CTXz/Not-so-Tiny-Dimmer/src/strip.h

          /*
   * Copyright (C) 2020  Patrick Pedersen

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
   * Author: Patrick Pedersen <ctx.xda@gmail.com>
   * Description: Exposes hardware abstraction routines for the LED strip.
   * 
   */

#pragma once

#include <stdbool.h>
#include <stdint.h>

#include <avr/eeprom.h>

#include "config.h"

#define R 0
#define G 1
#define B 2

#define RGB 0
#define GRB 1
#define BRG 2
#define BGR 3

#if STRIP_TYPE == WS2812

        extern uint16_t eeprom_strip_size EEMEM;
        extern uint16_t strip_size;

        #define SET_STRIP_SIZE(size) eeprom_update_word(&eeprom_strip_size, size)
        
        #ifdef STRIP_SIZE
                #define GET_STRIP_SIZE STRIP_SIZE
        #else
                #define GET_STRIP_SIZE (eeprom_read_word(&eeprom_strip_size))
        #endif
        
        #if WS2812_COLOR_ORDER == RGB
                #define WS2812_WIRING_RGB_0 0
                #define WS2812_WIRING_RGB_1 1
                #define WS2812_WIRING_RGB_2 2
        #elif WS2812_COLOR_ORDER == GRB
                #define WS2812_WIRING_RGB_0 1
                #define WS2812_WIRING_RGB_1 0
                #define WS2812_WIRING_RGB_2 2
        #elif WS2812_COLOR_ORDER == BRG
                #define WS2812_WIRING_RGB_0 2
                #define WS2812_WIRING_RGB_1 0
                #define WS2812_WIRING_RGB_2 1
        #elif WS2812_COLOR_ORDER == BGR
                #define WS2812_WIRING_RGB_0 2
                #define WS2812_WIRING_RGB_1 1
                #define WS2812_WIRING_RGB_2 0
        #else
                #error "No color order specified! Please set the WS2812_COLOR_ORDER directive in the config file!"
        #endif

#else

        #if NON_ADDR_STRIP_R == PB0
                #define NON_ADDR_STRIP_R_OCR OCR0A
        #elif NON_ADDR_STRIP_R == PB1
                #define NON_ADDR_STRIP_R_OCR OCR0B
        #elif NON_ADDR_STRIP_R == PB4
                #define NON_ADDR_STRIP_R_OCR OCR1B
        #else
                #error "Red LED pin does not support PWM! Please use PB0, PB1 or PB4!"
        #endif

        #if NON_ADDR_STRIP_G == PB0
                #define NON_ADDR_STRIP_G_OCR OCR0A
        #elif NON_ADDR_STRIP_G == PB1
                #define NON_ADDR_STRIP_G_OCR OCR0B
        #elif NON_ADDR_STRIP_G == PB4
                #define NON_ADDR_STRIP_G_OCR OCR1B
        #else
                #error "Green LED pin does not support PWM! Please use PB0, PB1 or PB4!"
        #endif

        #if NON_ADDR_STRIP_B == PB0
                #define NON_ADDR_STRIP_B_OCR OCR0A
        #elif NON_ADDR_STRIP_B == PB1
                #define NON_ADDR_STRIP_B_OCR OCR0B
        #elif NON_ADDR_STRIP_B == PB4
                #define NON_ADDR_STRIP_B_OCR OCR1B
        #else
                #error "Blue LED pin does not support PWM! Please use PB0, PB1 or PB4!"
        #endif

#endif

////////////////////////
// Data Structures
////////////////////////

/* RGB_t
 * ----------
 * Description:
 *      A simple three byte long array that
 *      stores RGB color values.
 */
typedef uint8_t RGB_t[3];
typedef uint8_t* RGB_ptr_t;

/* RGBbuf
 * ----------
 * Description:
 *      A primitve array of RGB_t objects.
 *      Must be allocated first! To project
 *      RGB buffers onto the stirp, use
 *      strip_apply_RGBbuf.
 * 
 *      WARNING: RGB buffers are very memory intensive,
 *      especially on bigger strips. Please consider using 
 *      other data structures if possible! If access of single
 *      pixels is required, please consider using the pxlbuf data
 *      structure!
 *      
 *      The required memory for a RGB buffer is given by:
 * 
 *              mem = RGB buffer size * sizeof(RGB_t) = RGB buffer size * 3
 * 
 *      Meaning if one were to fill a strip of 100 pixels with a RGB buffer, a
 *      total of 300 Bytes of memory would be necessary. This, toghether with
 *      the required memory for the firmware would exceed an ATtiny's memory
 *      size.  
 *            
 */
typedef RGB_t* RGBbuf;

/* substrp
 * ----------
 * Description:
 *      Reverses a given amount of pixels (length) and sets them
 *      to a specific color (rgb).
 *            
 */
typedef struct substrp {
        uint16_t length;
        RGB_t rgb;
} substrp;

/* substrpbuf
 * ----------
 * Description:
 *      Buffer of substrips. Substrips are projected
 *      in their indexed order. If the substrips do
 *      not cover the entire strip, the remaining
 *      pixels are set to off.
 *      Must be allocated first!
 * 
 *      Also see:
 *              substrpbuf_cpy
 *              substrpbuf_free
 *            
 */
typedef struct substrpbuf {
        uint16_t n_substrps;
        substrp *substrps;
} substrpbuf;

/* pxl
 * ----------
 * Description:
 *      Addresses a pixel at any given position (pos)
 *      and sets its color to the provided RGB value (rgb).
 *            
 */
typedef struct pxl {
        uint16_t pos;
        RGB_t rgb;
} pxl;

/* pxlbuf
 * ----------
 * Description:
 *      Buffer of pxl objects. Allows one to address
 *      pixels individually without having to allocate
 *      memory for unused pixels.
 *      
 *      The following helper functions should be used
 *      when working with pixel buffers:
 *      
 *              pxbuf_init
 *              pxbuf_insert
 *              pxbuf_exists
 *              pxbuf_remove
 *              pxbuf_remove_at
 *                 
 */
typedef struct pxbuf {
        uint16_t size;
        pxl* buf;
} pxbuf;

void rgb_apply_brightness(RGB_t rgb, uint8_t brightness);
void substripbuf_apply_brightness(substrpbuf *strp, uint8_t brightness);

void substrpbuf_cpy(substrpbuf *dst, substrpbuf *src);
void substrpbuf_free(substrpbuf *strp);

void pxbuf_init(pxbuf *buf);
void pxbuf_insert(pxbuf *buf, uint16_t pos, RGB_t rgb);
bool pxbuf_exists(pxbuf *buf, uint16_t pos);
void pxbuf_remove(pxbuf *buf, uint16_t index);
bool pxbuf_remove_at(pxbuf *buf, uint16_t pos);

void strip_apply_all(RGB_ptr_t rgb);

#if STRIP_TYPE == WS2812
void strip_calibrate();
void strip_apply_substrpbuf(substrpbuf strp);
void strip_apply_RGBbuf(RGBbuf RGBbuf);
void strip_apply_pxbuf(pxbuf *buf);
void strip_distribute_rgb(RGB_t rgb[], uint16_t size);
#endif

void strip_scroll_rgb(uint16_t val, uint8_t brightness);
bool strip_fade(RGB_ptr_t rgb, uint16_t delay_ms, uint8_t step_size, bool start);
bool strip_breathe(RGB_ptr_t rgb, uint16_t delay_ms, uint8_t step_size);
void strip_breathe_array(RGB_t rgb[], uint8_t size, uint16_t delay_ms, uint8_t step_size);
void strip_breathe_random(uint16_t delay_ms, uint8_t step_size);
void strip_breathe_rainbow(uint16_t delay_ms, uint8_t breath_step_size, uint8_t rgb_step_size);
void strip_rainbow(uint8_t step_size, uint16_t delay, uint8_t brightness);

#if STRIP_TYPE == WS2812
void strip_rotate_rainbow(uint8_t step_size, uint16_t delay_ms);
void strip_rain(RGB_t rgb, uint16_t max_drops, uint16_t min_t_appart, uint16_t max_t_appart, uint16_t delay);
bool strip_override(RGB_t rgb, uint16_t delay);
void strip_override_array(RGB_t rgb[], uint8_t size, uint16_t delay);
void strip_override_rainbow(uint16_t delay, uint8_t step_size);
#endif
